Kampi/Dock-HW/production/dock-CHECKED/HTML/images/cat_pdf_drill_map_ZSWatch-Dock-NPTH_drill_map.png

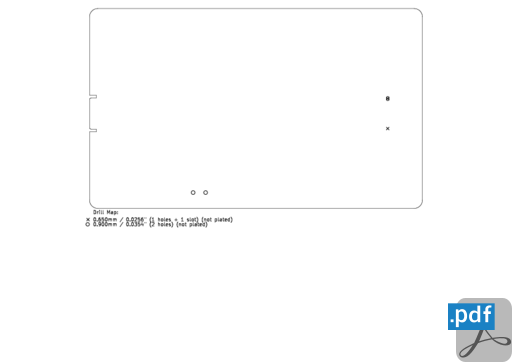
production/dock-CHECKED/HTML/images/cat_pdf_drill_map_ZSWatch-Dock-NPTH_drill_map.png
