Kampi/Dock-HW/production/dock-CHECKED/HTML/images/cat_png_3d_viewer_angled_bottom_ZSWatch-Dock-angled_bottom.png

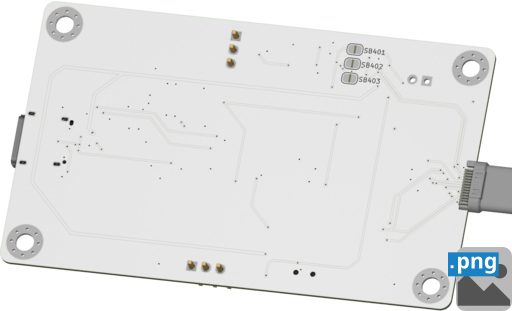
production/dock-CHECKED/HTML/images/cat_png_3d_viewer_angled_bottom_ZSWatch-Dock-angled_bottom.png
