Kampi/Dock-HW/production/dock-CHECKED/HTML/images/cat_png_3d_viewer_bottom_ZSWatch-Dock-bottom.png

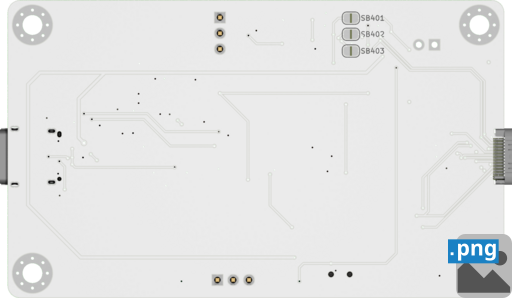
production/dock-CHECKED/HTML/images/cat_png_3d_viewer_bottom_ZSWatch-Dock-bottom.png
