Kampi/Dock-HW/production/dock-CHECKED/HTML/images/cat_pdf_fabrication_ZSWatch-Dock-fabrication.png

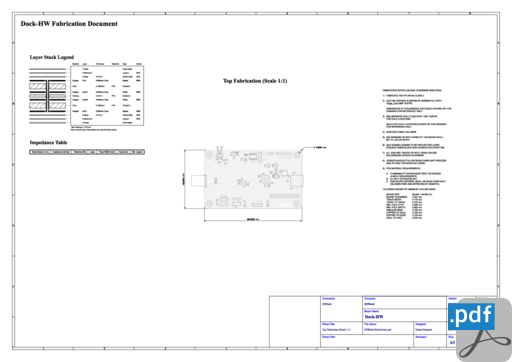
production/dock-CHECKED/HTML/images/cat_pdf_fabrication_ZSWatch-Dock-fabrication.png
